WChinmay/TrackingDogHarness/Documentation/Exterior Enclosure Dimensions.pdf

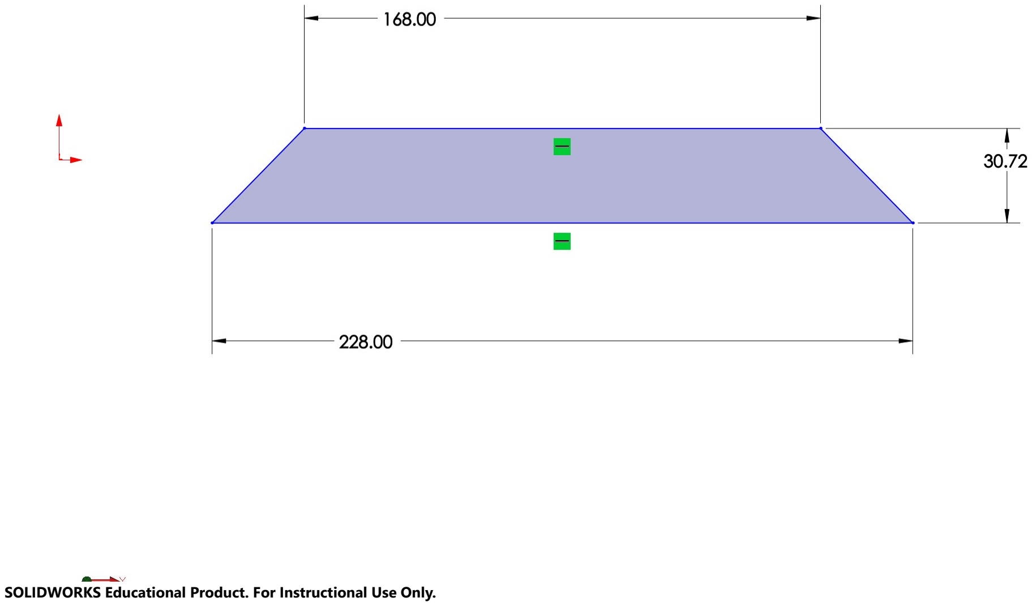
[picture p11: page 1]

SOLIDWORKS Educational Product. For Instructional Use Only.
