WChinmay/TrackingDogHarness/Documentation/Top Level Block Diagram.pdf

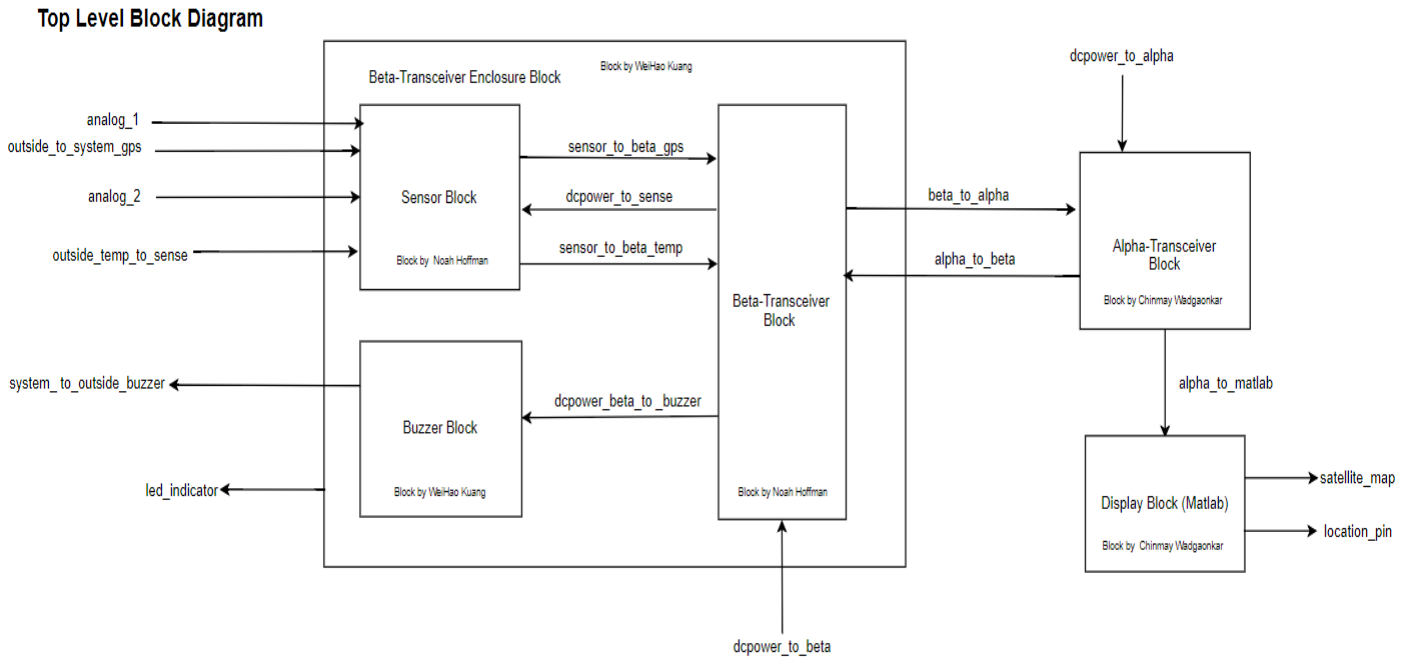
[picture p12: figure]
